palmerr23/Teensy8x8AudioBoard/Board Files/Main Board - Rev M/Rev M Board.png

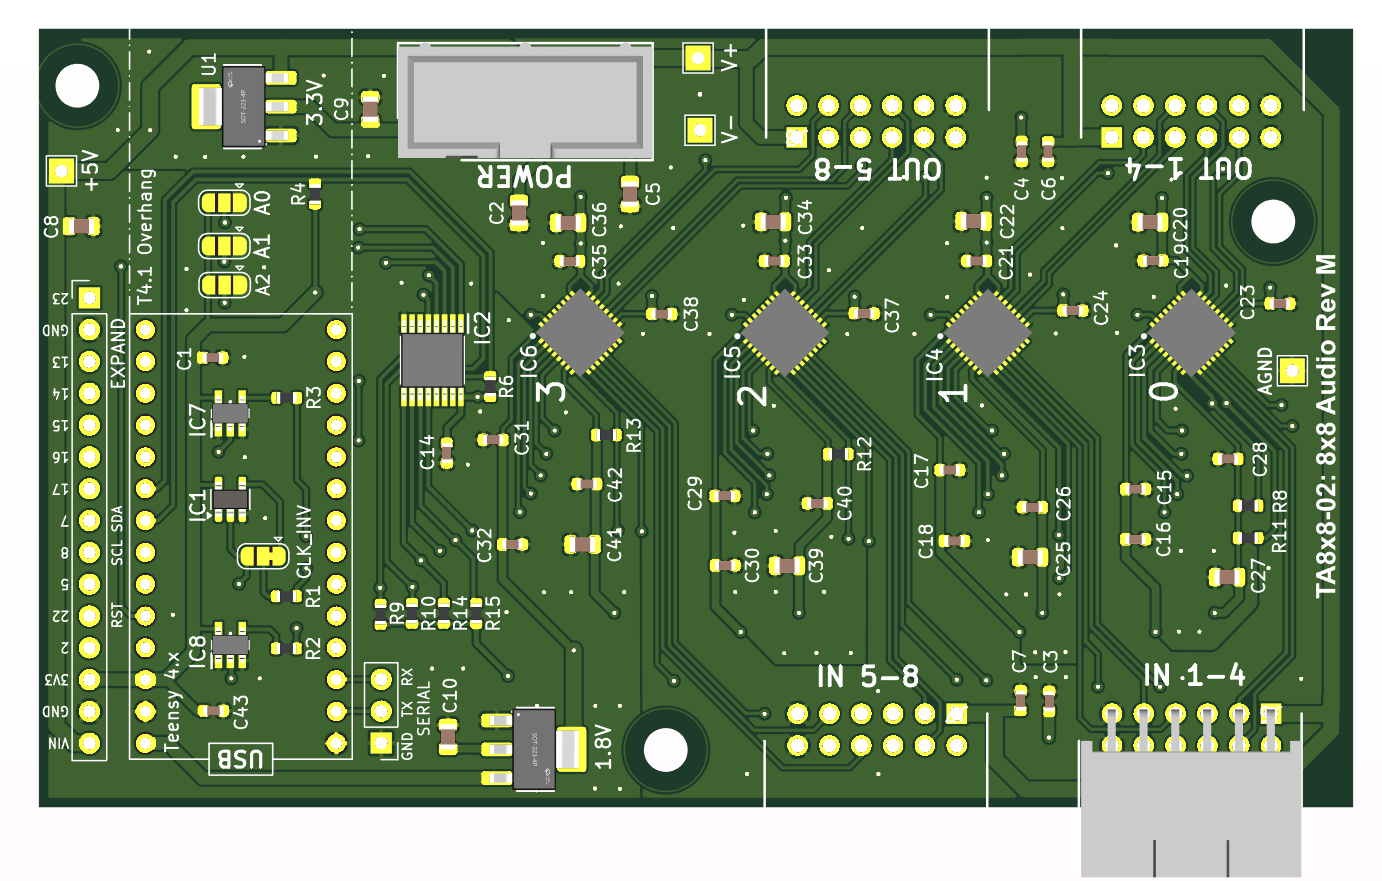
Board Files/Main Board - Rev M/Rev M Board.png
